flemingt/project-helena/3D Printing files/U1MB near final.stl

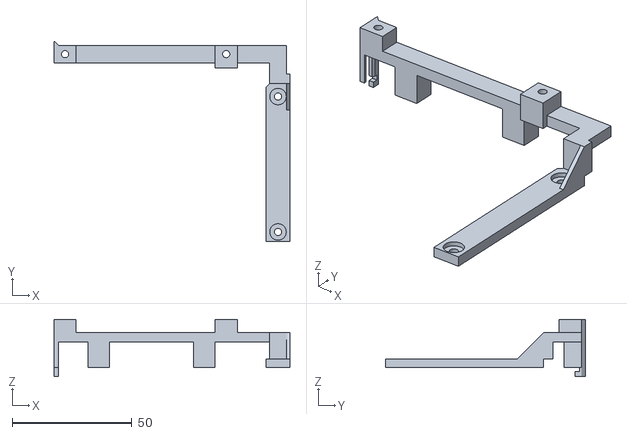
[picture p19: CAD file, 2022-04-11]
3D Printing files/U1MB near final.stl
98.5 x 83.5 x 23.8
