flemingt/project-helena/3D Printing files/Cherry to stackpole Final.stl

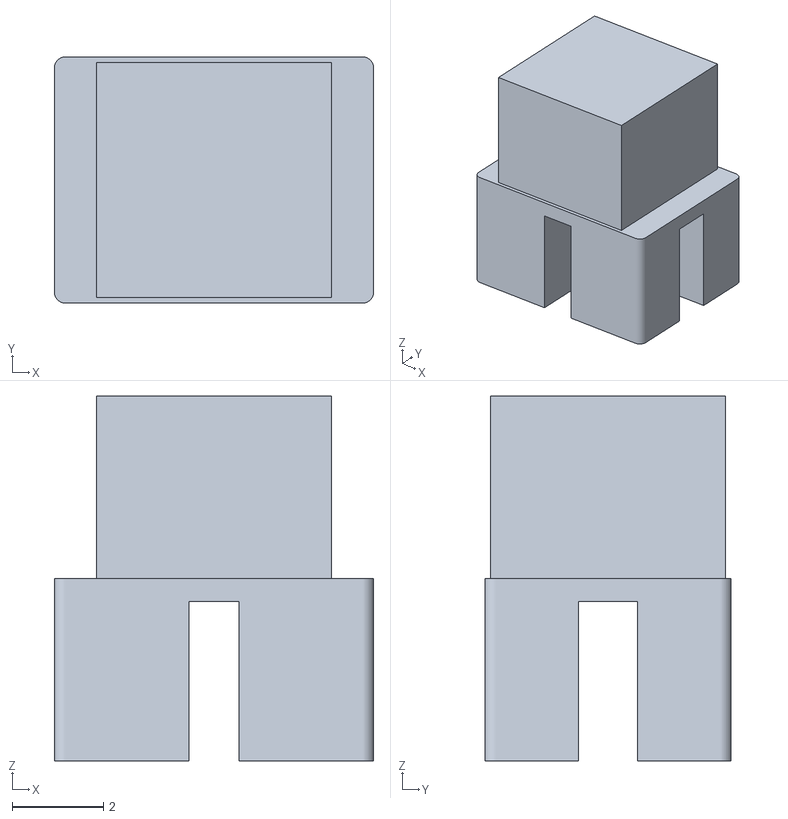
[picture p20: CAD file, 2022-04-11]
3D Printing files/Cherry to stackpole Final.stl
7.00 x 5.40 x 8.00
